fila95/Gaia/Actions Map.mindnode/QuickLook/Preview.jpg

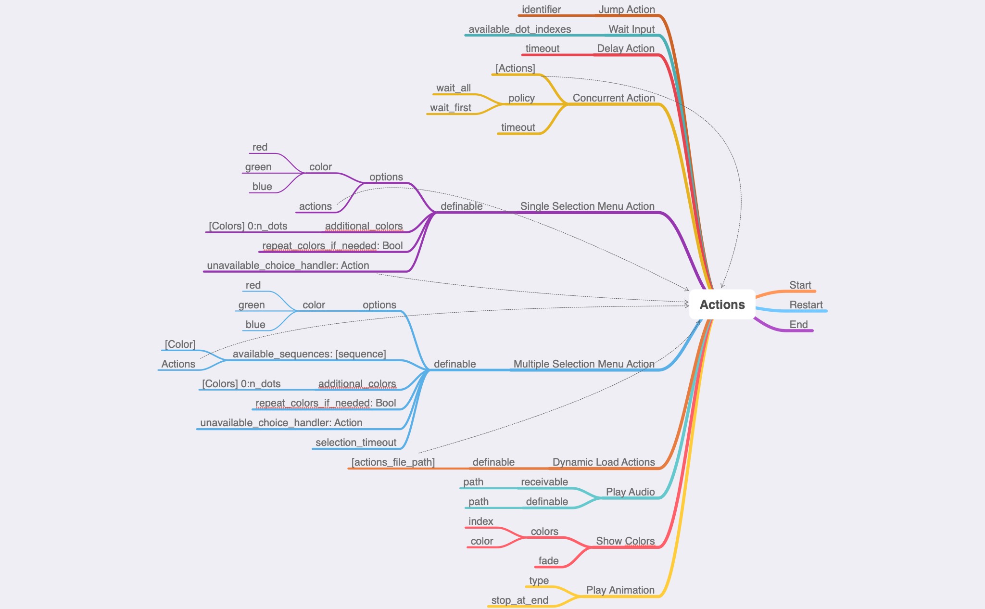
Actions Map.mindnode/QuickLook/Preview.jpg
