fila95/Gaia/Assets/Renders/Dot_3.0_2019-Jan-18_07-37-19PM-000_CustomizedView3860034832_jpg.jpg

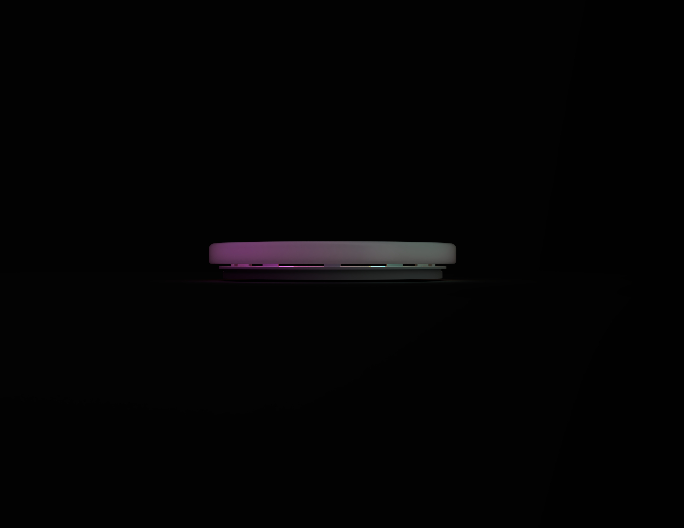
Assets/Renders/Dot_3.0_2019-Jan-18_07-37-19PM-000_CustomizedView3860034832_jpg.jpg
