fila95/Gaia/Assets/Renders/Dot_3.0_2019-Jan-18_07-38-34PM-000_CustomizedView43123195816_jpg.jpg

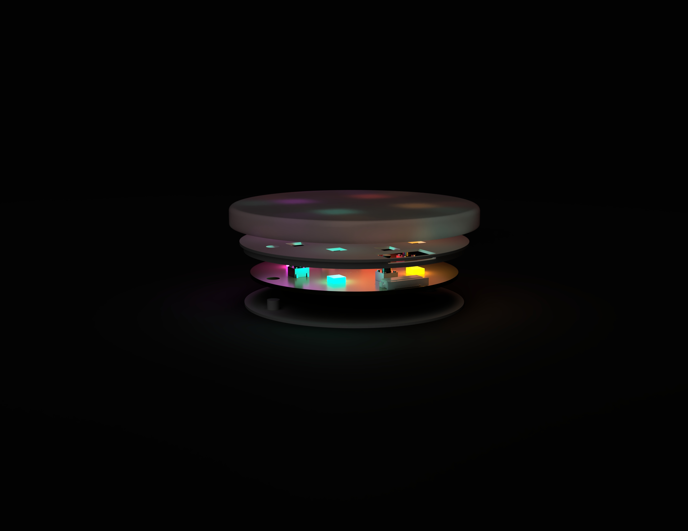
Assets/Renders/Dot_3.0_2019-Jan-18_07-38-34PM-000_CustomizedView43123195816_jpg.jpg
