fila95/Gaia/Assets/Renders/Dot_3.0_2019-Jan-18_07-39-06PM-000_CustomizedView31684099001_jpg.jpg

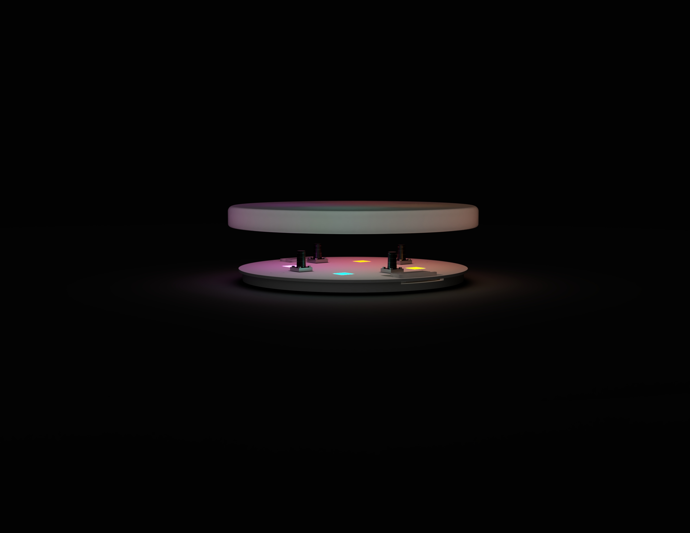
Assets/Renders/Dot_3.0_2019-Jan-18_07-39-06PM-000_CustomizedView31684099001_jpg.jpg
