fila95/Gaia/Assets/Renders/Dot_3.0_Renders_2019-Jan-18_07-45-34PM-000_CustomizedView29843571925_jpg.jpg

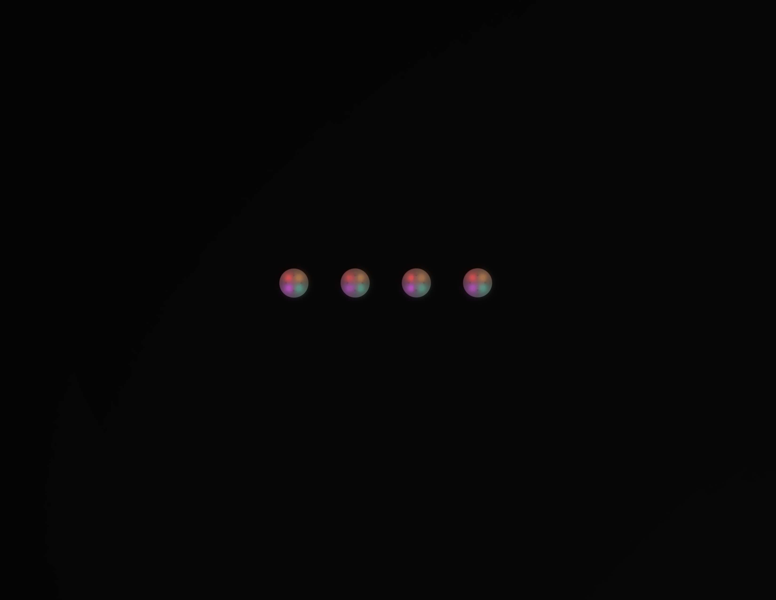
Assets/Renders/Dot_3.0_Renders_2019-Jan-18_07-45-34PM-000_CustomizedView29843571925_jpg.jpg
