fila95/Gaia/Assets/Renders/Dot_3.0_Renders_2019-Jan-18_07-45-47PM-000_CustomizedView10146333075_jpg.jpg

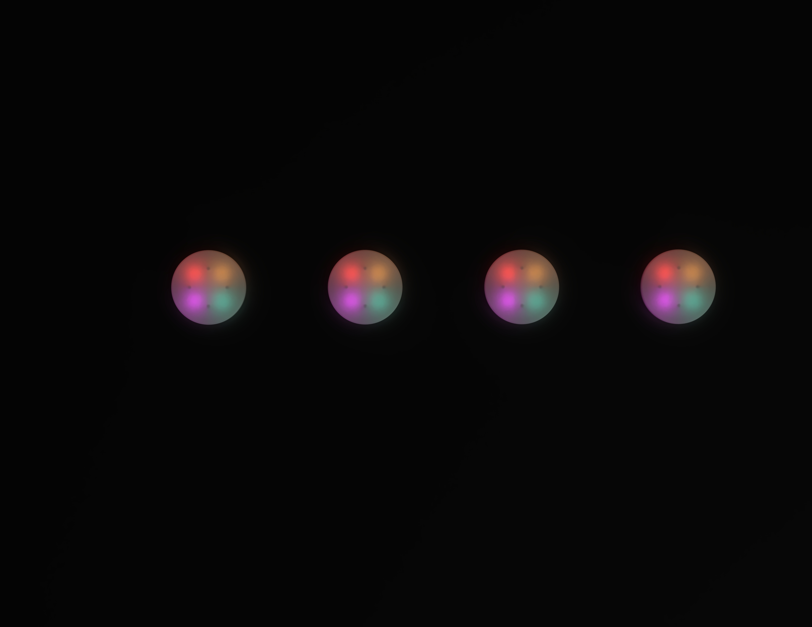
Assets/Renders/Dot_3.0_Renders_2019-Jan-18_07-45-47PM-000_CustomizedView10146333075_jpg.jpg
