fila95/Gaia/Assets/Renders/Dot_3.0_Renders_2019-Jan-18_07-46-01PM-000_CustomizedView1292036104_jpg.jpg

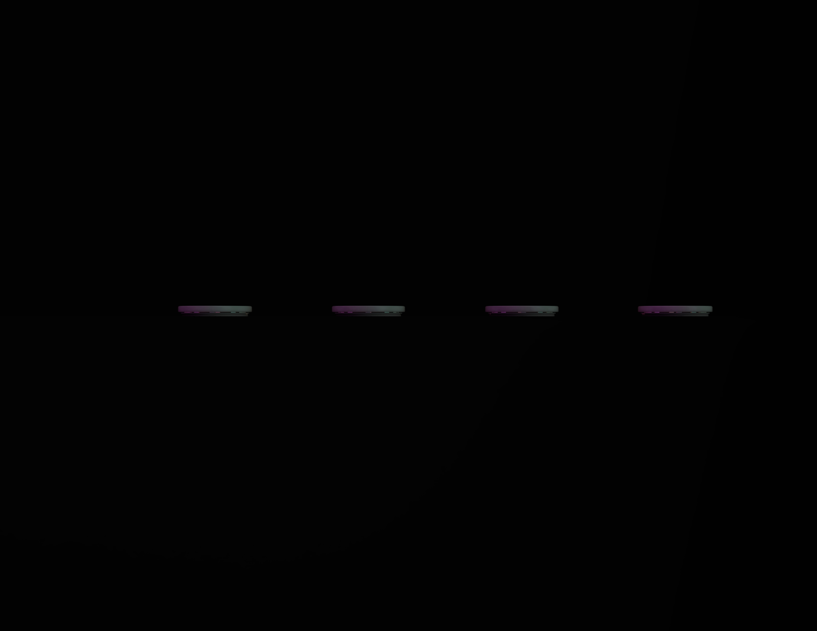
Assets/Renders/Dot_3.0_Renders_2019-Jan-18_07-46-01PM-000_CustomizedView1292036104_jpg.jpg
