fila95/Gaia/Assets/Renders/Dot_3.0_Renders_2019-Jan-18_07-46-14PM-000_CustomizedView11523125525_jpg.jpg

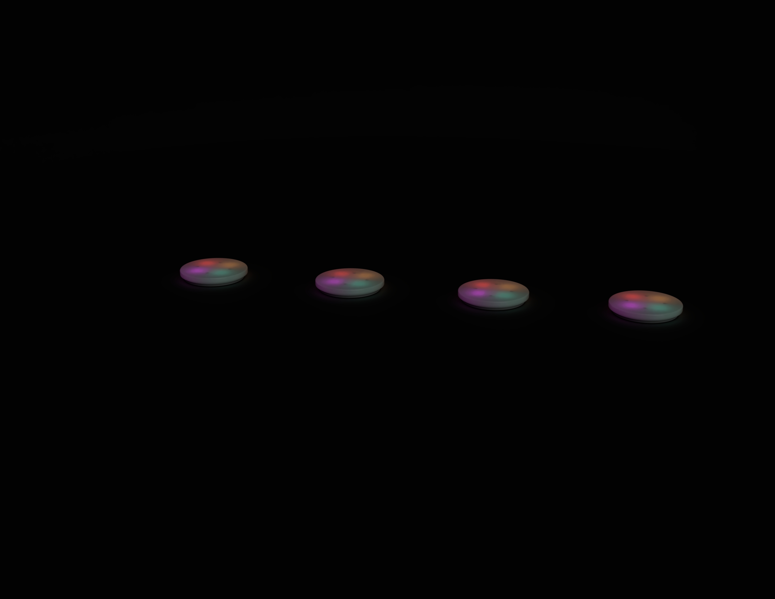
Assets/Renders/Dot_3.0_Renders_2019-Jan-18_07-46-14PM-000_CustomizedView11523125525_jpg.jpg
