fila95/Gaia/Assets/Renders/normal_1.jpg

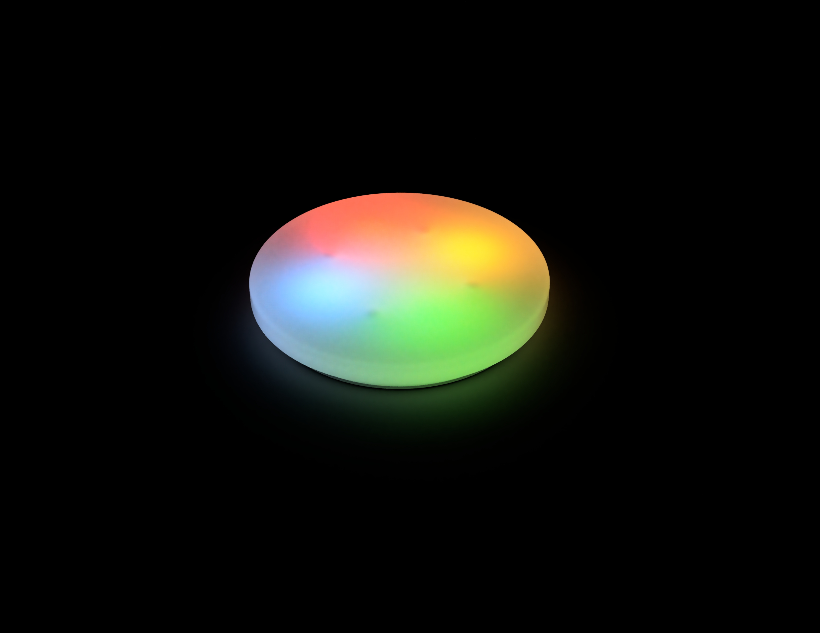
Assets/Renders/normal_1.jpg
