fila95/Gaia/Assets/Build/Build Process/c8fb4657-eab7-4fd8-a2a8-340a585826e8.JPG

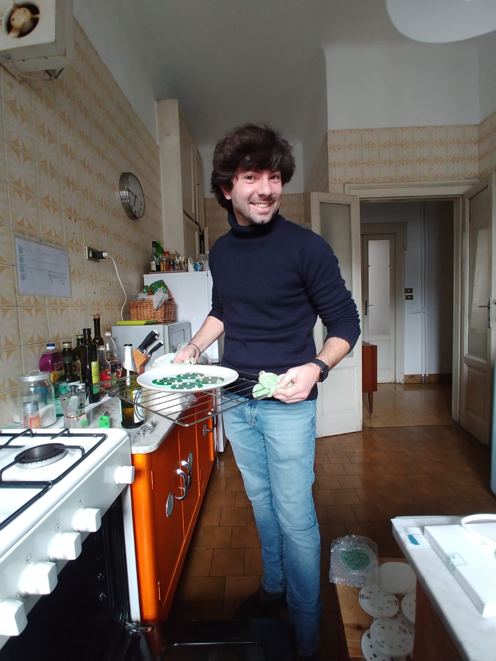
Assets/Build/Build Process/c8fb4657-eab7-4fd8-a2a8-340a585826e8.JPG
