fila95/Gaia/Assets/Build/Build Process/IMG_3586.jpg

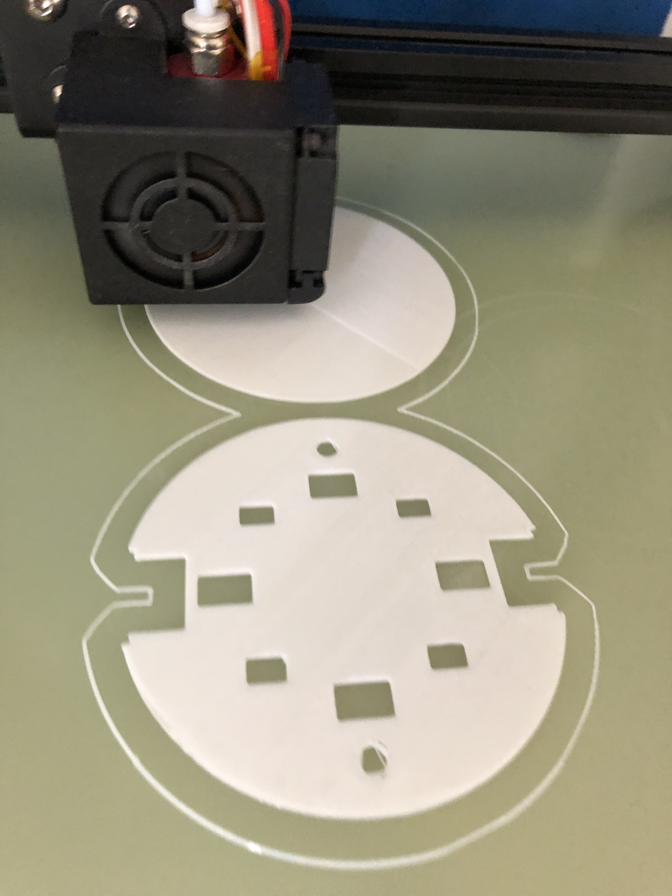
Assets/Build/Build Process/IMG_3586.jpg
