fila95/Gaia/Assets/Build/Build Process/IMG_3701.jpg

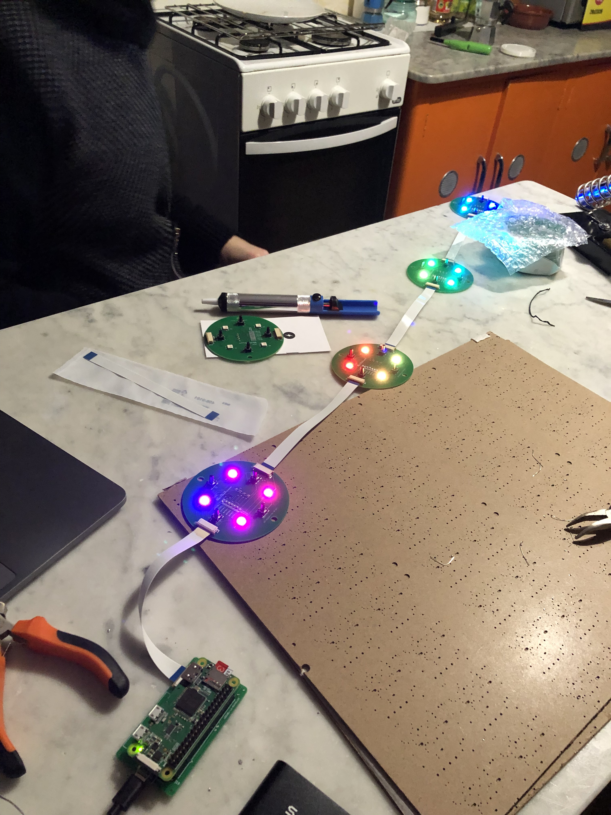
Assets/Build/Build Process/IMG_3701.jpg
