fila95/Gaia/Assets/Build/Build Process/IMG_4813.jpg

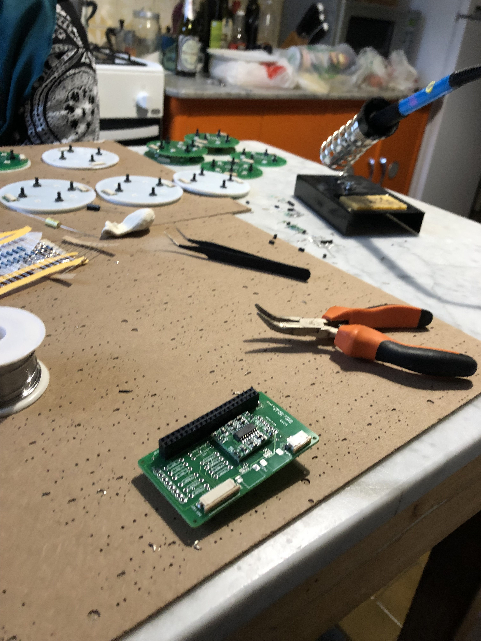
Assets/Build/Build Process/IMG_4813.jpg
