fila95/Gaia/Assets/Build/Build Process/IMG_7243.jpg

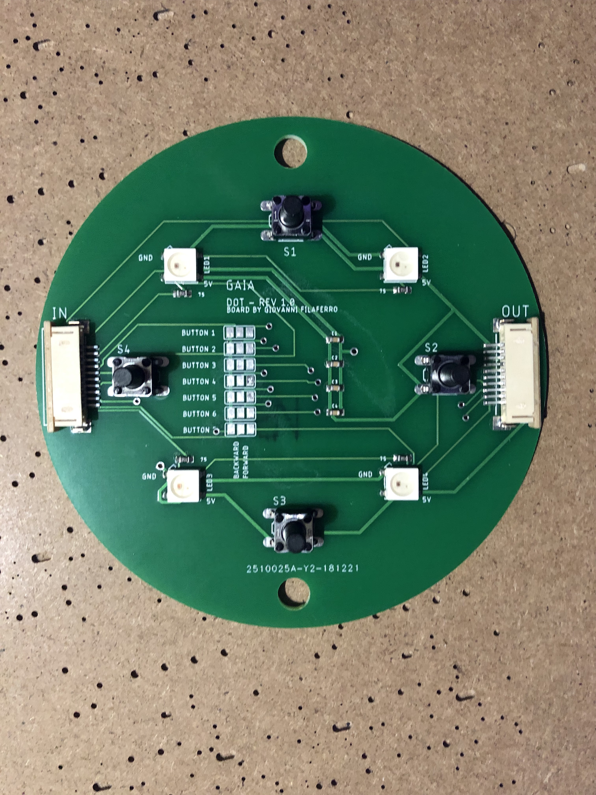
Assets/Build/Build Process/IMG_7243.jpg
