fila95/Gaia/services/scripts/geki/dots/Dot.py

from .DotColor import DotColor
from .DotColor import Colors
from .DotWorker import DotWorker

import pigpio
import logging
import threading
import time
from queue import Queue, Empty
try:
	from neopixel import *
except ImportError as e:
	from .neopixel_mock import Adafruit_NeoPixel, Color

class Dot:
	LED_COUNT = 4

	def __init__(self, strip, led_start_index, button_pin, cb, stopAnimationTrigger):
		self.__strip = strip
		self.__cb = cb
		self.__stopAnimationTrigger = stopAnimationTrigger
		self.__led_start_index = int(led_start_index)
		self.__button_pin = int(button_pin)
		self.__targetColor = DotColor(255, 255, 255)
		self.__currentColor = self.__targetColor
		self.__targetBrightnessedColor = self.__targetColor
		self.__brightness = 255

		self.queue = Queue()
		self.interrupt_event = threading.Event()
		self.stop_event = threading.Event()

		self._worker = DotWorker(logging, self.__strip, self.queue, self.stop_event, self.interrupt_event)
		self._worker.start()

		self.__animating = False

		cb = pigpio.pi()
		cb.callback(self.__button_pin, edge=0, func=self.__callback)
		cb.set_glitch_filter(self.__button_pin, steady=250)
		self.__showColor(self.__targetColor)

	def getColor(self):
		return self.__targetColor

	def getBrightnessAppliedColor(self):
		return self.__targetBrightnessedColor

	def setColor(self, color: DotColor, fade=True, stopGlobalAnimation=True):
		if stopGlobalAnimation:
			self.__stopAnimationTrigger()

		if fade:
			self.__clearQueue()
		
		# logging.info("Setting color of dot:{:d} to r: {:d}, g: {:d}, b: {:d}.".format(self.__led_start_index, color.red, color.green, color.blue))
		self.__targetColor = color
		self.__showColor(color, fade=fade)


	def setBrightness(self, brightness: int, fade=True, stopGlobalAnimation=True):
		if stopGlobalAnimation:
			self.__stopAnimationTrigger()
		
		if fade:
			self.__clearQueue()
		
		# logging.info("Setting brightness of dot:{:d} to {:d}.".format(self.__led_start_index, brightness))
		self.__brightness = max(0, min(brightness, 255))
		if self.__targetColor is not None:
			self.setColor(self.__targetColor, fade=fade)

	# --- Private
	def __showColor(self, color: DotColor, fade=False):
		# Normalize brightness
		col = color
		if isinstance(col, Colors):
			col = color.value
		self.__targetBrightnessedColor = self.__generateBrightnessedColorFrom(col)

		if fade is False:
			self.__currentColor = self.__targetBrightnessedColor
			for i in range(self.__led_start_index, self.__led_start_index+self.LED_COUNT):
				self.__strip.setPixelColor(i, Color(self.__currentColor.red, self.__currentColor.green, self.__currentColor.blue))
			self.__strip.show()
		else:
			self.__run_fade_animation()
			pass

	# FADE
	def __handle_async(self, lfunc, interrupt=True):
		# ql = self.queue.qsize()
		if(interrupt == True and not self.queue.empty() and not self.interrupt_event.isSet()):
			self.interrupt_event.set()
		self.queue.put(lfunc)

	def __run_fade_animation(self):
		self.__animating = True
		lfunc = self.__fade
		self.__handle_async(lfunc, True)
	
	# ** ASYNC **
	def __generateBrightnessedColorFrom(self, color):
		bright = float(self.__brightness) / 255
		red = int(float(color.red) * bright)
		green = int(float(color.green) * bright)
		blue = int(float(color.blue) * bright)
		col = DotColor(red=red, green=green, blue=blue)
		return col

	def __fade(self, wait_ms=10, iterations=10):
		"""Fade Colors."""
		# if self.__led_start_index == 0:
		# 	print(self.__targetBrightnessedColor.red, self.__targetBrightnessedColor.green, self.__targetBrightnessedColor.blue)
		# 	print("fade_start")

		col = self.__currentColor
		r_diff =  int((self.__targetBrightnessedColor.red - col.red)/iterations)
		g_diff = int((self.__targetBrightnessedColor.green - col.green)/iterations)
		b_diff = int((self.__targetBrightnessedColor.blue - col.blue)/iterations)

		for j in range(iterations):

			col = self.__currentColor
			red = col.red + r_diff
			green = col.green + g_diff
			blue = col.blue + b_diff

			self.__currentColor = DotColor(red=red, green=green, blue=blue)
			for i in range(self.__led_start_index, self.__led_start_index+self.LED_COUNT):
				self.__strip.setPixelColor(i, Color(self.__currentColor.red, self.__currentColor.green, self.__currentColor.blue))
			self.__strip.show()

			# if self.__led_start_index == 0:
			# 	print(red, green, blue)

			time.sleep(wait_ms/1000.0)

		
		# Fix last color
		time.sleep(wait_ms/1000.0)
		self.__currentColor = self.__targetBrightnessedColor
		for i in range(self.__led_start_index, self.__led_start_index+self.LED_COUNT):
			self.__strip.setPixelColor(i, Color(self.__currentColor.red, self.__currentColor.green, self.__currentColor.blue))
		self.__strip.show()

		# if self.__led_start_index == 0:
		# 	print("fade_end")
		self.__animating = False

	
	def __close(self):
		#interrupt running task
		self.interrupt_event.set()
		#stop loop and end-thread
		self.stop_event.set()
		# self.__strip.__del__()

	def __clearQueue(self):
		#consume items first
		while not self.queue.empty():
			self.queue.get()
		#then interrupt thead
		if(self.__animating == True):
			self.interrupt_event.set()

	def __callback(self, gpio, newLevel, tick):
		if gpio == self.__button_pin:
			self.__cb(int(self.__led_start_index/self.LED_COUNT), self)
