fila95/Gaia/services/scripts/geki/Game.py

import logging
import threading

from dots import *
from sound.SpeakerManager import SpeakerManager
from actions.Action import Action
from actions.ActionParser import ActionParser
import os

class Game():

	def __init__(self):
		print("Initializing Geki Game...")
		self.leds = DotManager(tapHandler=self.__dotWasTapped)
		print("DotManager Loaded!")

		self.speakers = SpeakerManager(finishPlayingCallback=self.__musicDidFinishPlaying)
		print("SpeakerManager Loaded!")

		self.currentAction = None
		self.currentActionIndex = 0
		

	def start(self):
		self.availableActions = Action.actionParser().parse(filename="config/Action_elementari_2.json")
		self.currentActionIndex = -1
		self.nextAction()



	def stop(self):
		print("Stopping Geki Game...")
		self.leds.turnAllOff()
		self.speakers.deinit()

	def restart(self):
		self.start()

	# Actions:
	def nextAction(self, optionalParams=None):
		self.currentActionIndex += 1
		self.__deactivateCurrentAction()
		self.currentAction = self.availableActions[self.currentActionIndex]
		print("Starting Action \"{}\"".format(type(self.currentAction).__name__))
		self.__activateCurrentAction(optionalParams=optionalParams)

	def jumpToAction(self, id, optionalParams=None):
		act = None
		for a in self.availableActions:
			if a.identifier == id:
				act = a
				break

		if act is not None:
			self.__deactivateCurrentAction()
			self.currentAction = self.availableActions[self.currentActionIndex]
			print("Jumping to Action \"{}\"".format(type(self.currentAction).__name__))
			self.__activateCurrentAction(optionalParams=optionalParams)


	def produceActions(self, actions):
		insertableIndex = self.currentActionIndex+1
		for a in actions:
			self.availableActions.insert(insertableIndex, a)
			insertableIndex+=1

	def __deactivateCurrentAction(self):
		if self.currentAction is not None:
			self.currentAction._deactivate()

	def __activateCurrentAction(self, optionalParams=None):
		if self.currentAction is not None:
			self.currentAction._activate(game=self, optionalParams=optionalParams)

	# Dots:
	def __dotWasTapped(self, index, dot):
		color = dot.getColor()
		print("Tapped Dot at index: {} and color: r={}, g={}, b={}".format(index, color.red, color.green, color.blue))
		if self.currentAction is not None:
			self.currentAction.dotWasTapped(index, dot)
		pass

	# Music Playback:
	def __musicDidFinishPlaying(self):
		if self.currentAction is not None:
			self.currentAction.audioDidFinishPlaying()
