fila95/Gaia/Assets/Build/Build Process/IMG_0816.jpg

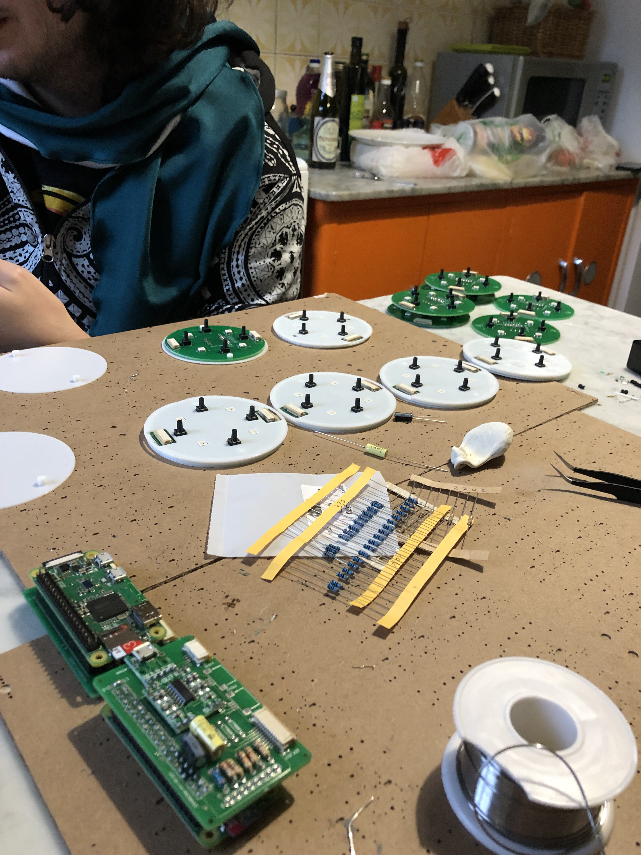
Assets/Build/Build Process/IMG_0816.jpg
