fila95/Gaia/Assets/Build/Build Process/IMG_9140.jpg

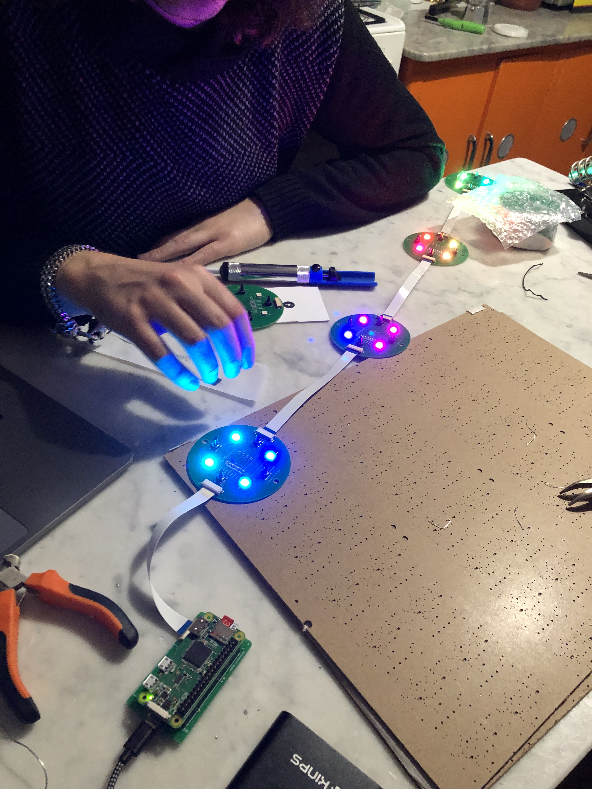
Assets/Build/Build Process/IMG_9140.jpg
